dragonlost/NAFABox-hardware/Doc/picture/Iso_compil.jpg

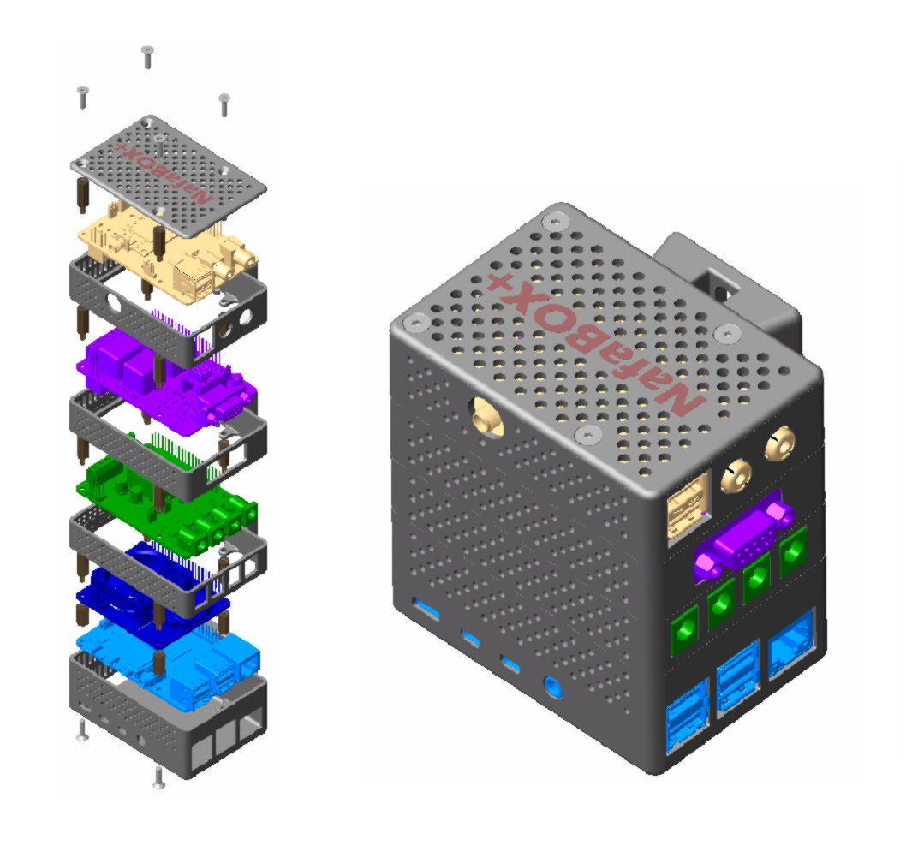
Doc/picture/Iso_compil.jpg
