dragonlost/NAFABox-hardware/Test/res images/pins_res_solder.png

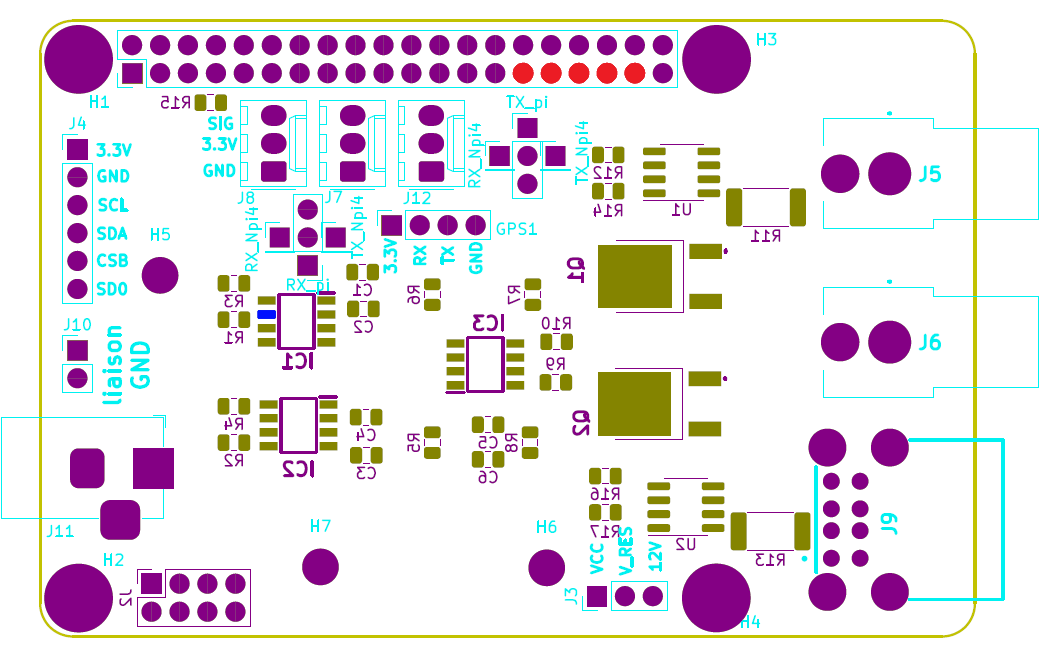
Test/res images/pins_res_solder.png
