dragonlost/NAFABox-hardware/Software/DS1050_lib.py

import smbus

add_pwm_up = 0x2a
add_pwm_down = 0x28


pas = 100 / (2 ** 5)

def set_pwm_DC(DEVICE_ADDRESS, DC):

    # open i2C bus number
    bus = smbus.SMBus(1)    # 0 = /dev/i2c-0 (port I2C0), 1 = /dev/i2c-1 (port I2C1)

    # write
    dec_pwm = int(DC / pas)

    if 32 >= dec_pwm >= 0:
        print("ok")
        if dec_pwm == 32:
            bus.write_byte(DEVICE_ADDRESS, 0x20)
            print("set : 100%")
        else:
            bus.write_byte(DEVICE_ADDRESS, dec_pwm)
            print("set : " + str(dec_pwm * pas)+"%")
    else:
        print("nope")

    bus.close()

    return dec_pwm


def read_pwm_DC(DEVICE_ADDRESS):

    # open i2C bus number
    bus = smbus.SMBus(1)    # 0 = /dev/i2c-0 (port I2C0), 1 = /dev/i2c-1 (port I2C1)

    # read
    DC = bus.read_byte(DEVICE_ADDRESS)
    print("data : " + str(DC * pas)+"%")

    bus.close()

    return DC


def set_Shutdown_mode(DEVICE_ADDRESS):

    # open i2C bus number
    bus = smbus.SMBus(1)    # 0 = /dev/i2c-0 (port I2C0), 1 = /dev/i2c-1 (port I2C1)

    # write
    bus.write_byte(DEVICE_ADDRESS, 0xC0)
    print("Shutdown ON")

    bus.close()

    return 1


def set_recall_mode(DEVICE_ADDRESS):

    # open i2C bus number
    bus = smbus.SMBus(1)    # 0 = /dev/i2c-0 (port I2C0), 1 = /dev/i2c-1 (port I2C1)

    # write
    bus.write_byte(DEVICE_ADDRESS, 0x80)
    print("Shutdown OFF")

    bus.close()

    return 1
